s-light/LEDBoard_Layout_SUN/mounting_sun/mounting_sun_arm.png

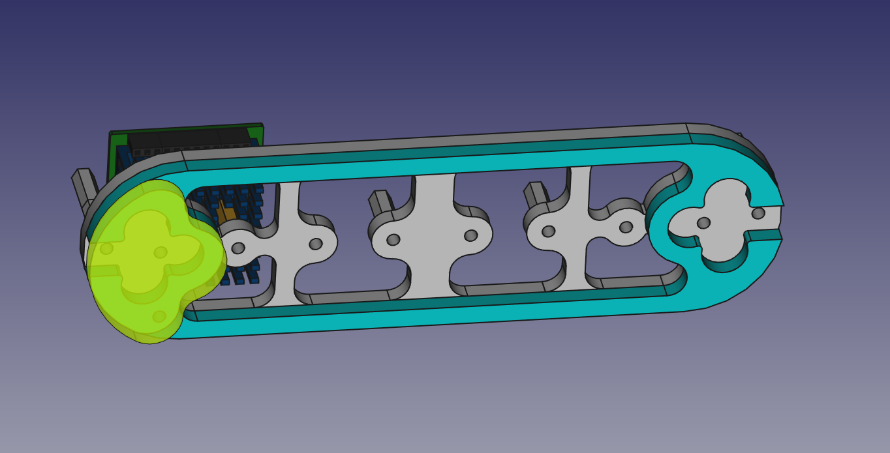
mounting_sun/mounting_sun_arm.png
