s-light/LEDBoard_Layout_SUN/photos/P1640706_small.jpg

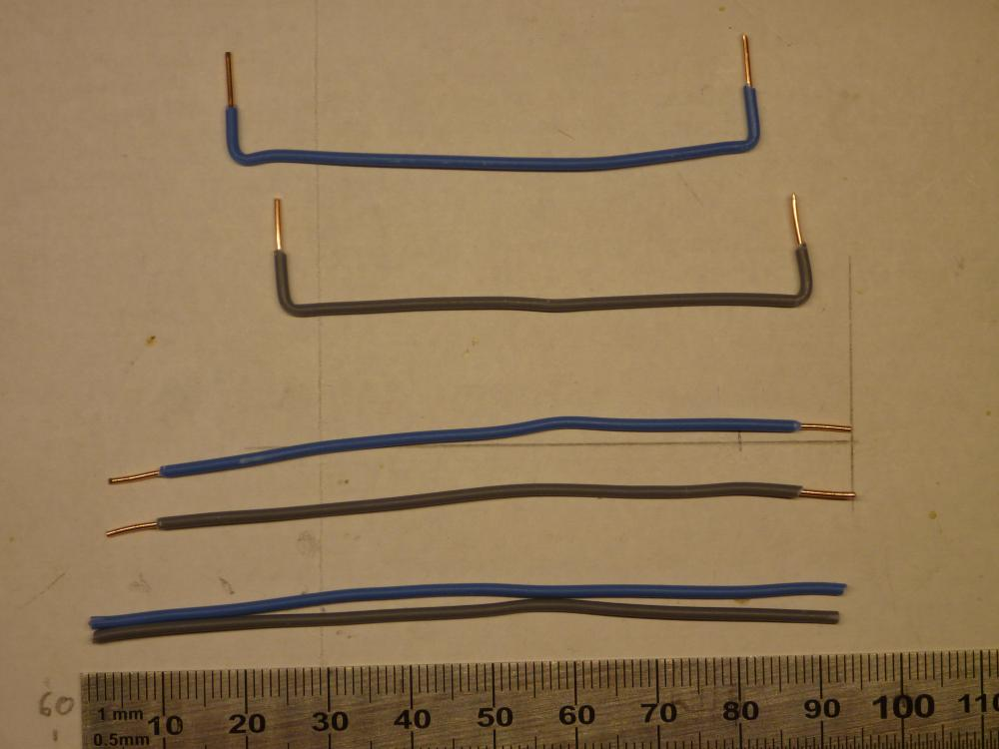
photos/P1640706_small.jpg
