s-light/LEDBoard_Layout_SUN/photos/P1650086_small.jpg

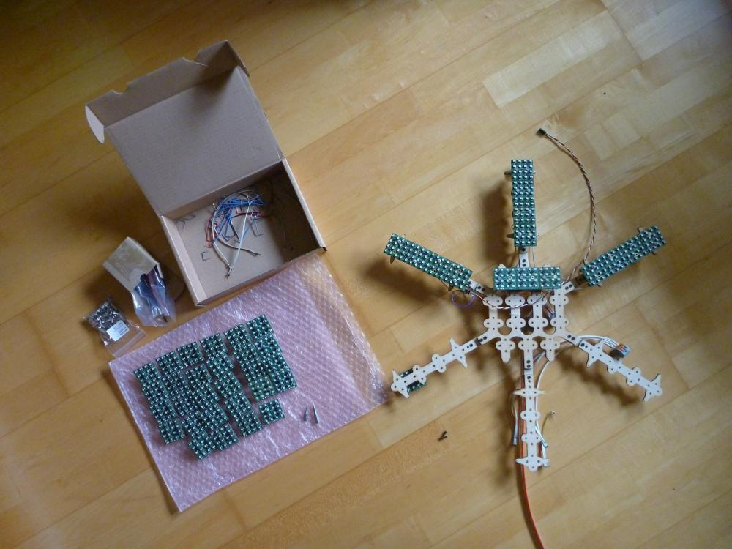
photos/P1650086_small.jpg
