s-light/LEDBoard_Layout_SUN/photos/P1650098_small.jpg

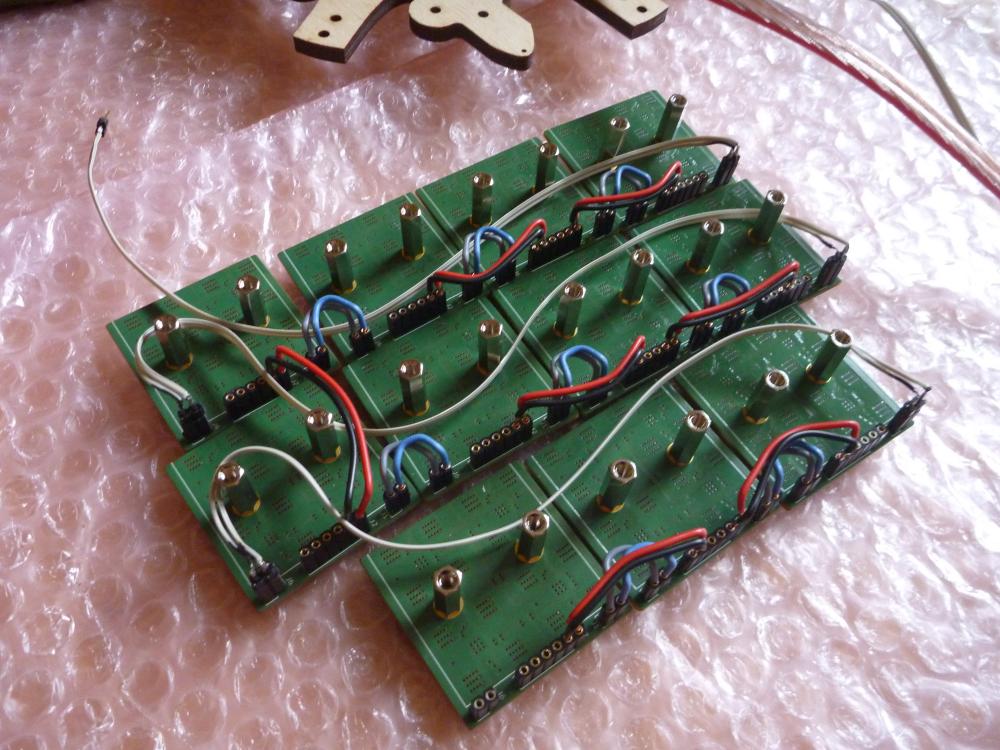
photos/P1650098_small.jpg
