s-light/LEDBoard_Layout_SUN/photos/P1650166_small2.jpg

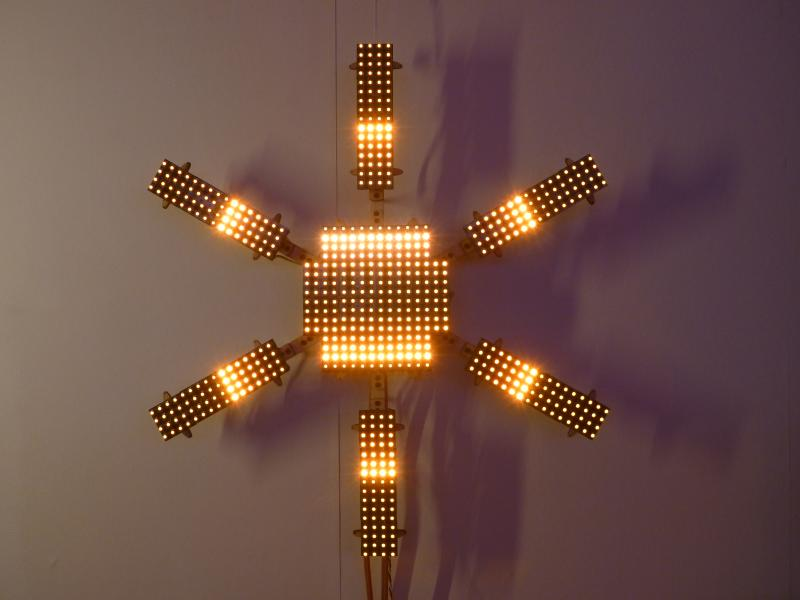
photos/P1650166_small2.jpg
