s-light/LEDBoard_Layout_SUN/photos/P1660830_small.jpg

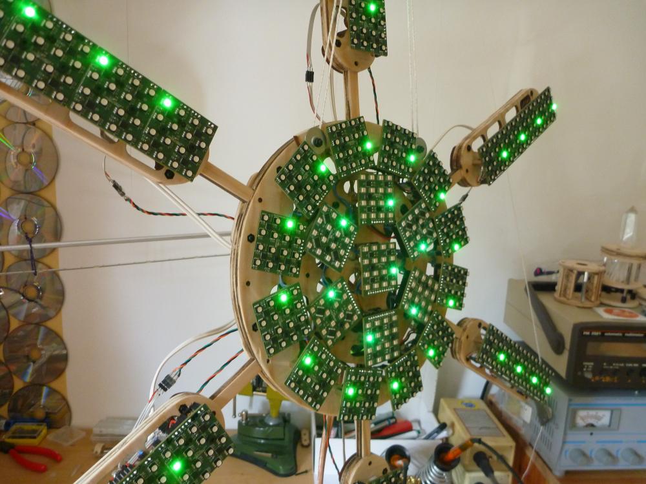
photos/P1660830_small.jpg
