s-light/LEDBoard_Layout_SUN/photos/P1660883_small.jpg

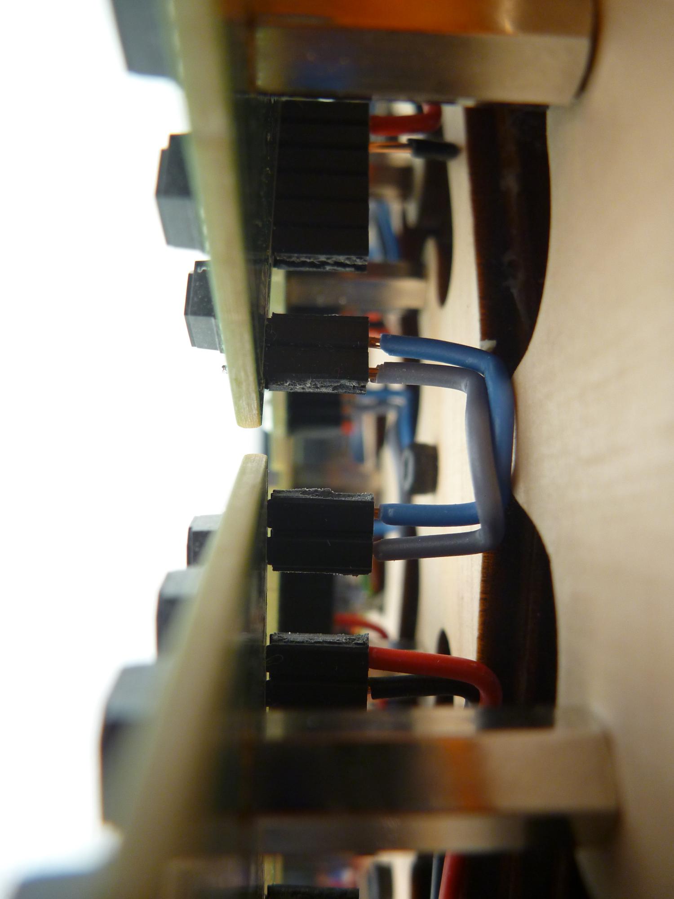
photos/P1660883_small.jpg
